The-Automation-Warehouse/Catch-The-Light/making of/Feet 1.jpg

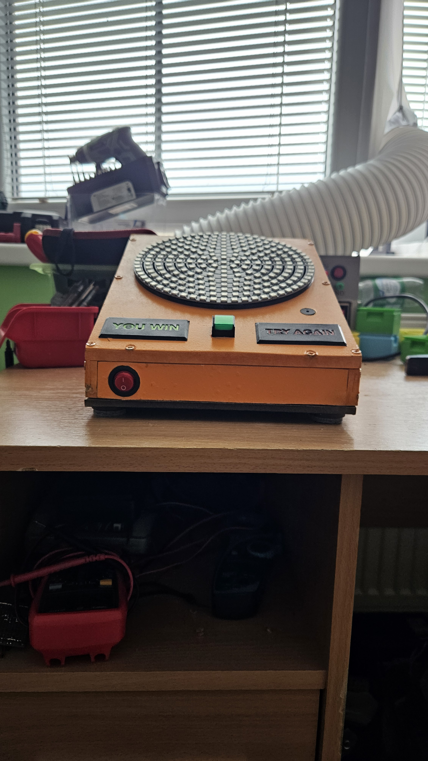
making of/Feet 1.jpg
