The-Automation-Warehouse/Catch-The-Light/making of/It works.jpg

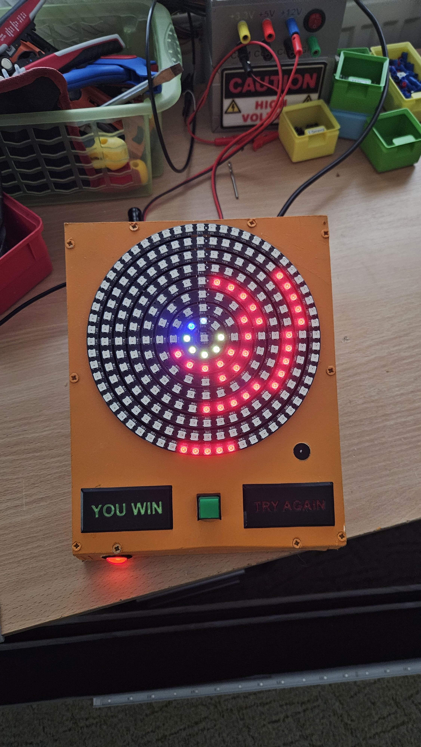
making of/It works.jpg
