The-Automation-Warehouse/Catch-The-Light/making of/Remaking leds.jpg

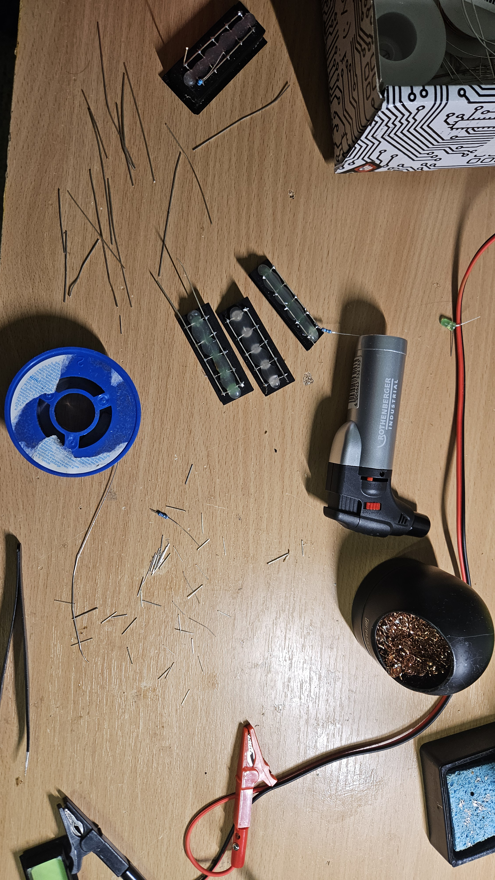
making of/Remaking leds.jpg
