The-Automation-Warehouse/Catch-The-Light/making of/Snapped front.jpg

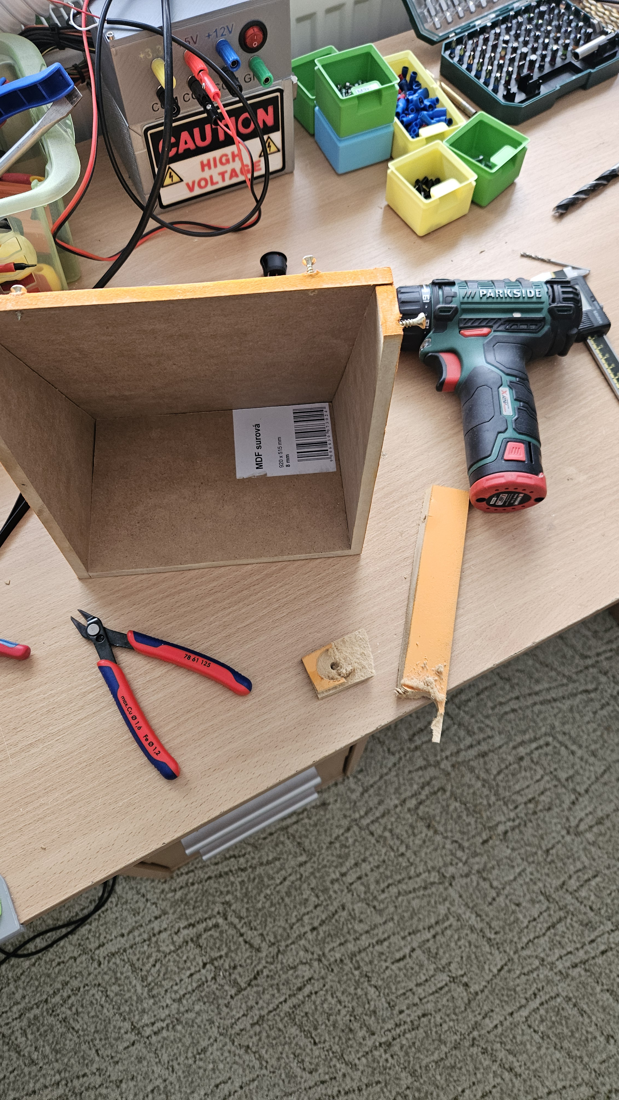
making of/Snapped front.jpg
