The-Automation-Warehouse/Catch-The-Light/making of/table mess.jpg

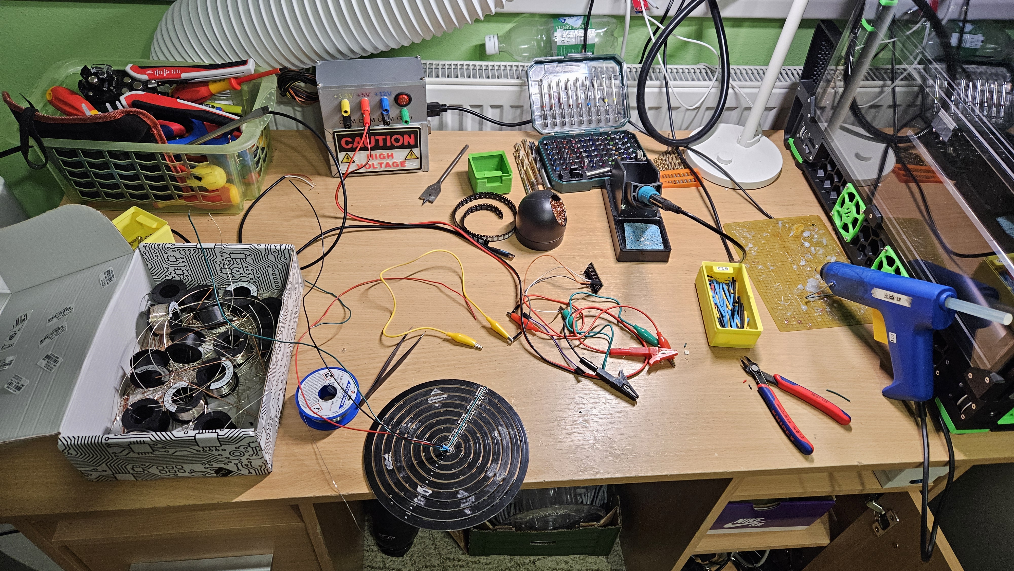
making of/table mess.jpg
