The-Automation-Warehouse/Catch-The-Light/making of/Text back.jpg

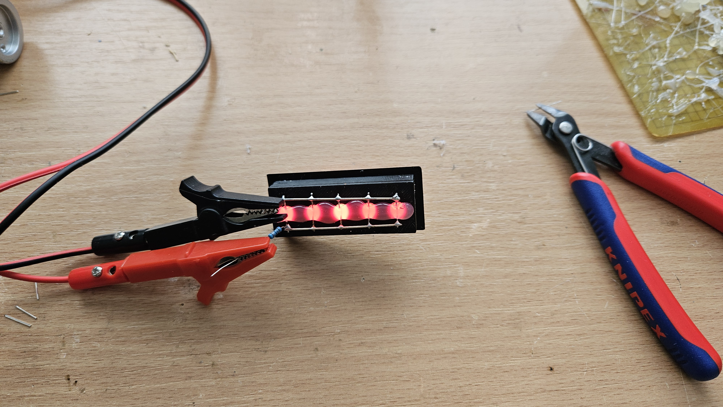
making of/Text back.jpg
