The-Automation-Warehouse/Catch-The-Light/making of/Backlit text.jpg

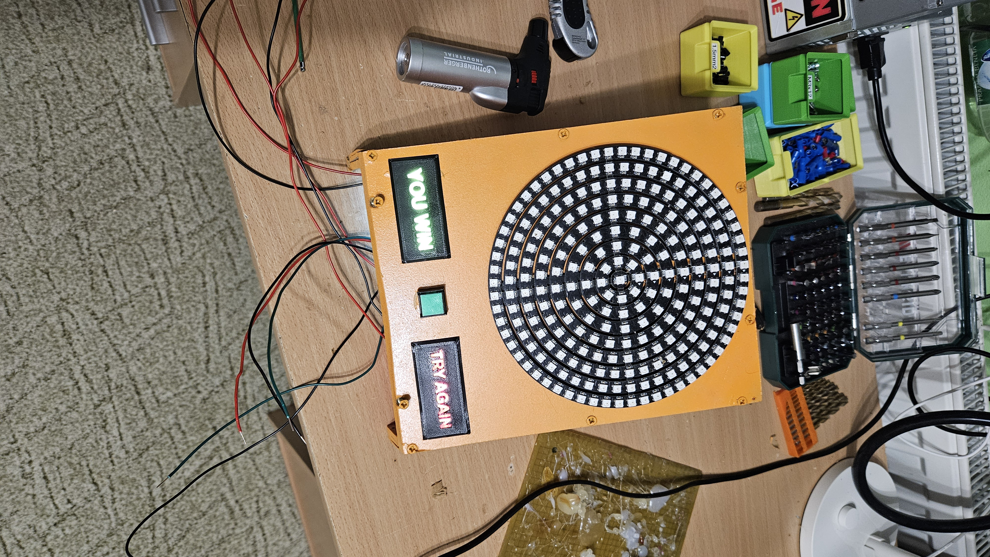
making of/Backlit text.jpg
