The-Automation-Warehouse/Catch-The-Light/making of/not working.jpg

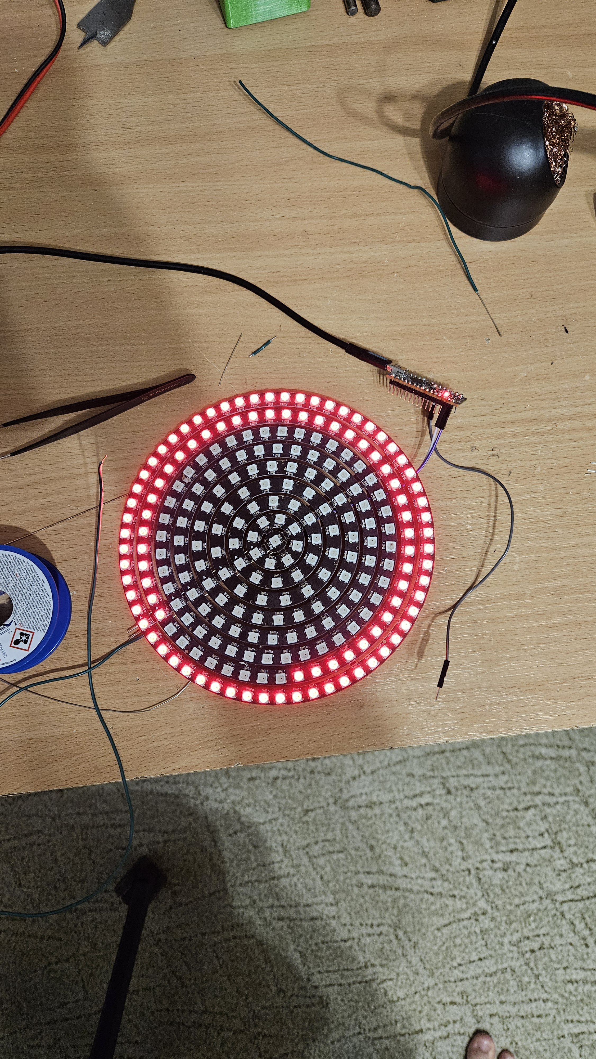
making of/not working.jpg
