The-Automation-Warehouse/Catch-The-Light/making of/Painted.jpg

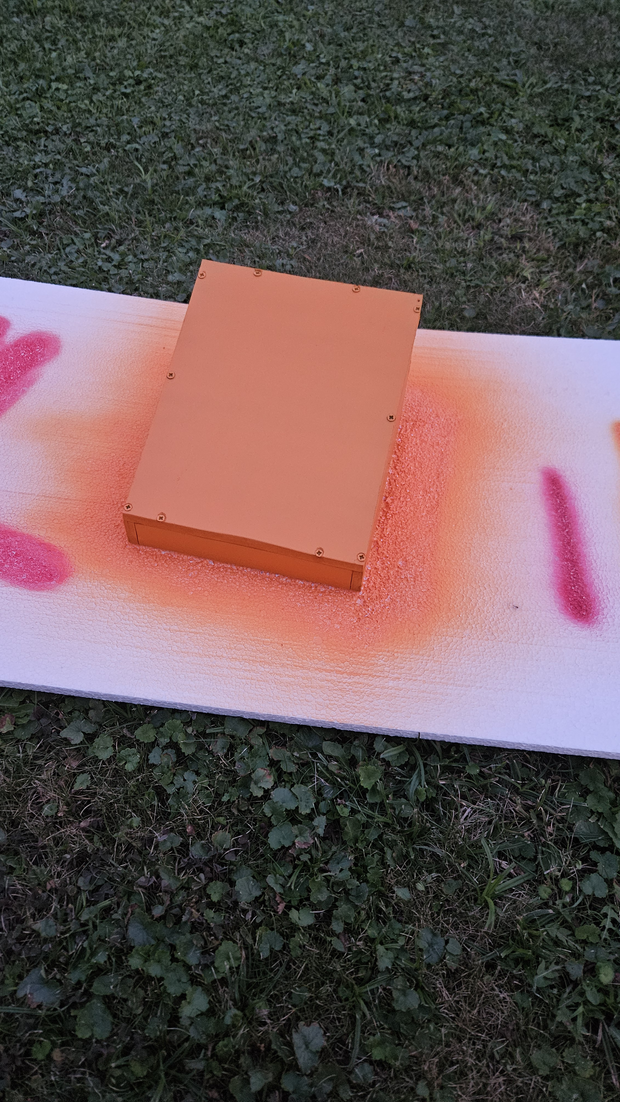
making of/Painted.jpg
