The-Automation-Warehouse/Catch-The-Light/making of/Wiring 1.jpg

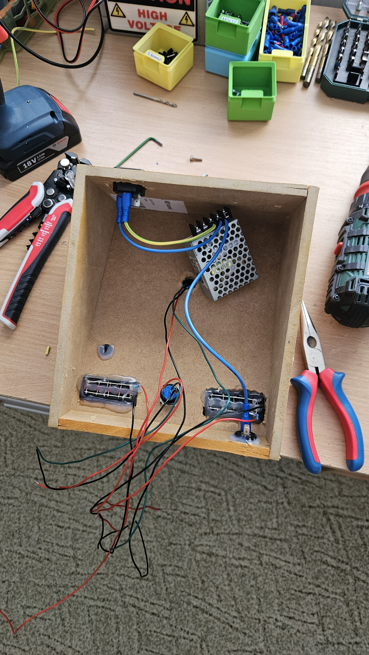
making of/Wiring 1.jpg
