The-Automation-Warehouse/Catch-The-Light/making of/Wiring 2.jpg

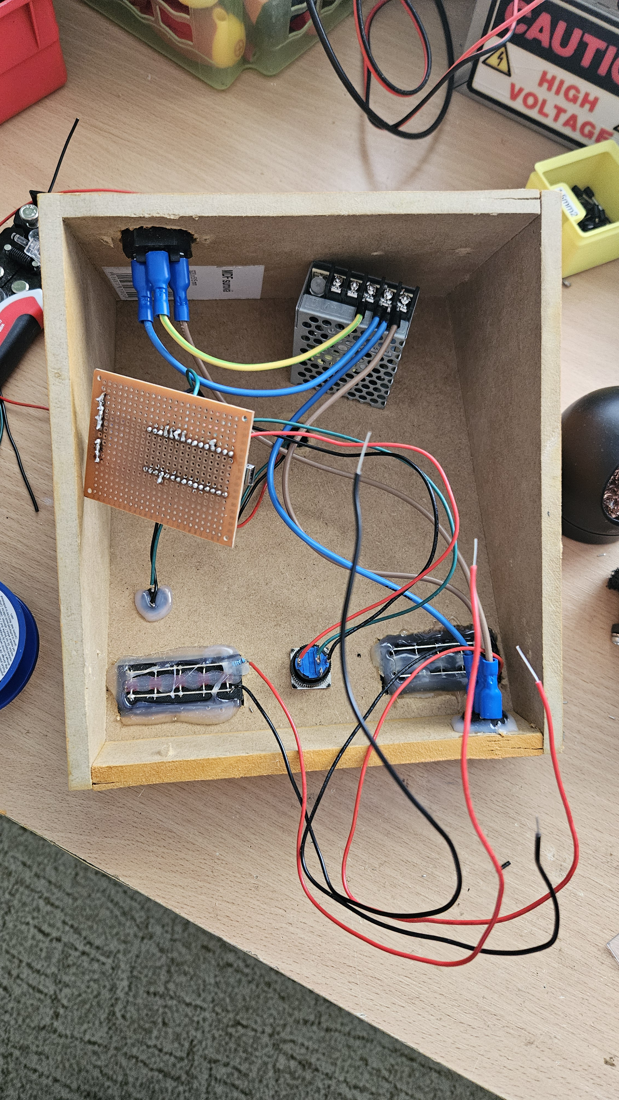
making of/Wiring 2.jpg
